jadebuilds/cattown/3d Print files/Gantry mount/top front gantry mount v0.02.3MF

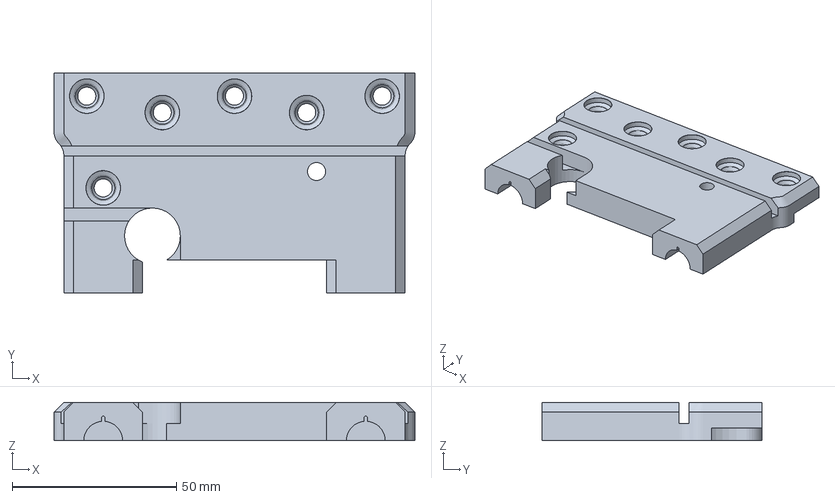
[picture p15: CAD file, 2024-06-08]
3d Print files/Gantry mount/top front gantry mount v0.02.3MF
110.0 x 67.0 x 11.7 mm
