jadebuilds/cattown/3d Print files/Tool head/Tool head V1.21.3MF

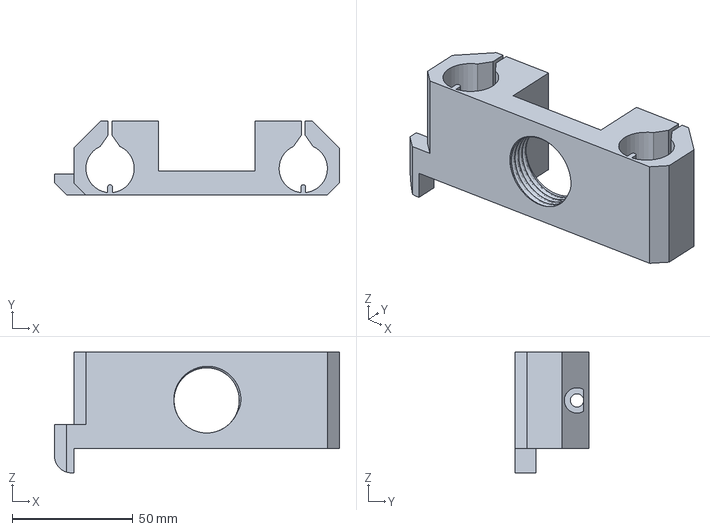
[picture p16: CAD file, 2024-06-08]
3d Print files/Tool head/Tool head V1.21.3MF
118.0 x 30.7 x 50.0 mm
