jadebuilds/cattown/3d Print files/Tool head/Belt holder v0.02.3MF

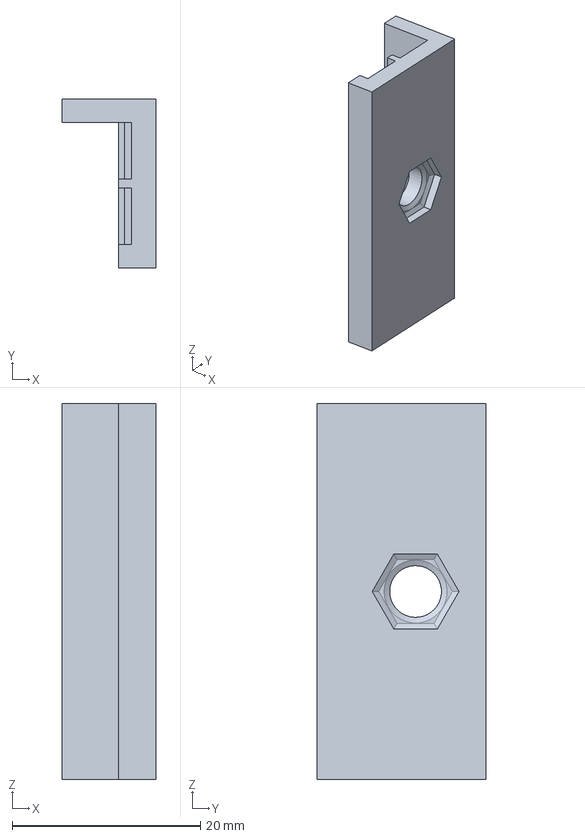
[picture p17: CAD file, 2024-06-08]
3d Print files/Tool head/Belt holder v0.02.3MF
10.0 x 18.0 x 40.0 mm
