jadebuilds/cattown/3d Print files/Tool head/Magnet holder v0.02.3MF

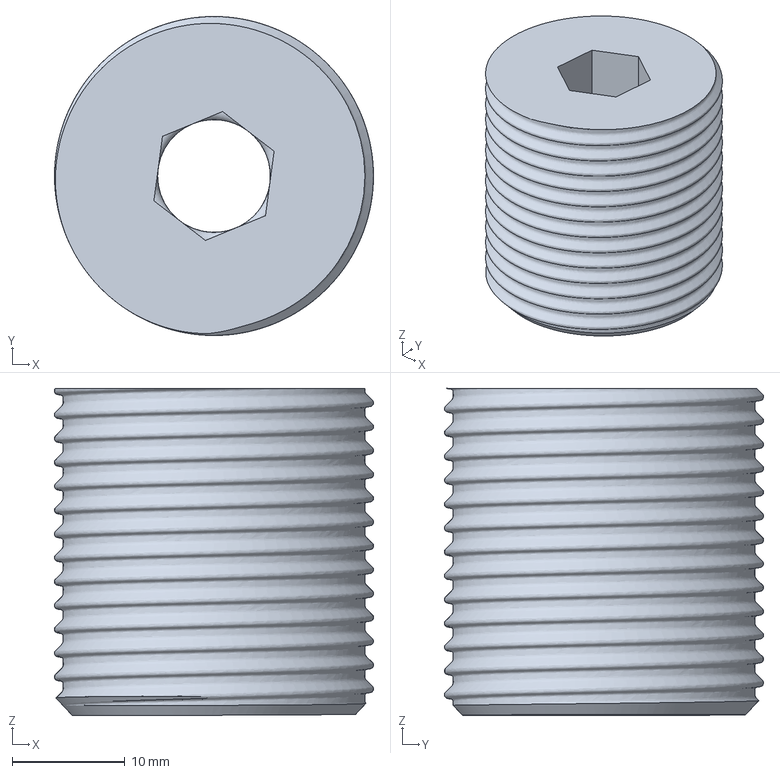
[picture p18: CAD file, 2024-06-08]
3d Print files/Tool head/Magnet holder v0.02.3MF
28.3 x 28.3 x 29.1 mm
