jadebuilds/cattown/3d Print files/Tool head/Bushing v0.07.3MF

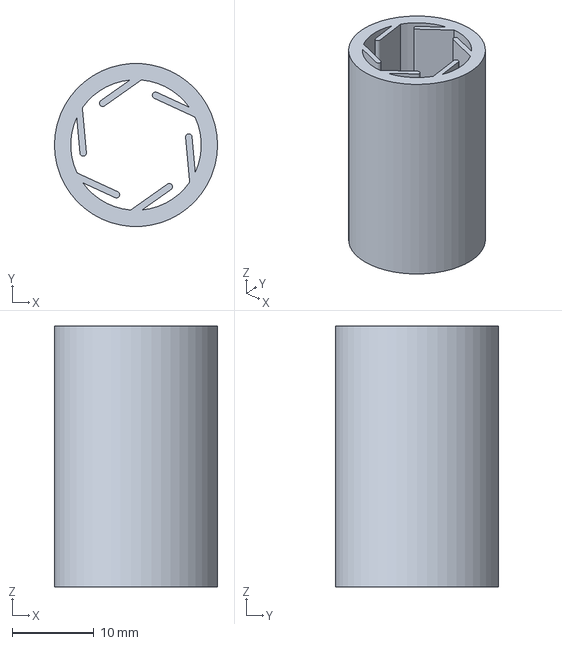
[picture p19: CAD file, 2024-06-08]
3d Print files/Tool head/Bushing v0.07.3MF
20.0 x 20.0 x 32.0 mm
