jadebuilds/cattown/3d Print files/Tool head/Bushing.3MF

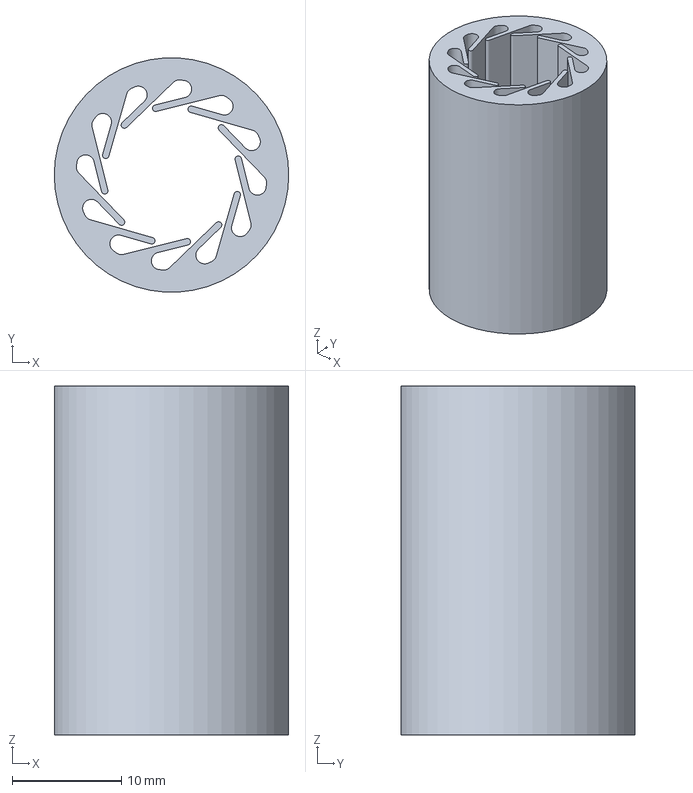
[picture p20: CAD file, 2024-06-08]
3d Print files/Tool head/Bushing.3MF
21.5 x 21.5 x 32.0 mm
