jadebuilds/cattown/firmware/v4_arduino/fixed_point.h

/* 
 * fixed_point.h
 * 
 * Contains specific handling for the Arduino Due microcontroller, including PWM.
 */

#include <stdint.h>

#ifndef FIXED_POINT_H
#define FIXED_POINT_H

typedef int32_t int_23q8;
typedef uint32_t uint_24q8;

#endif // FIXED_POINT_H
